petl/USB-C-cable-tester-C2C-caberQU/photos/v3/CaberQ_021.jpg

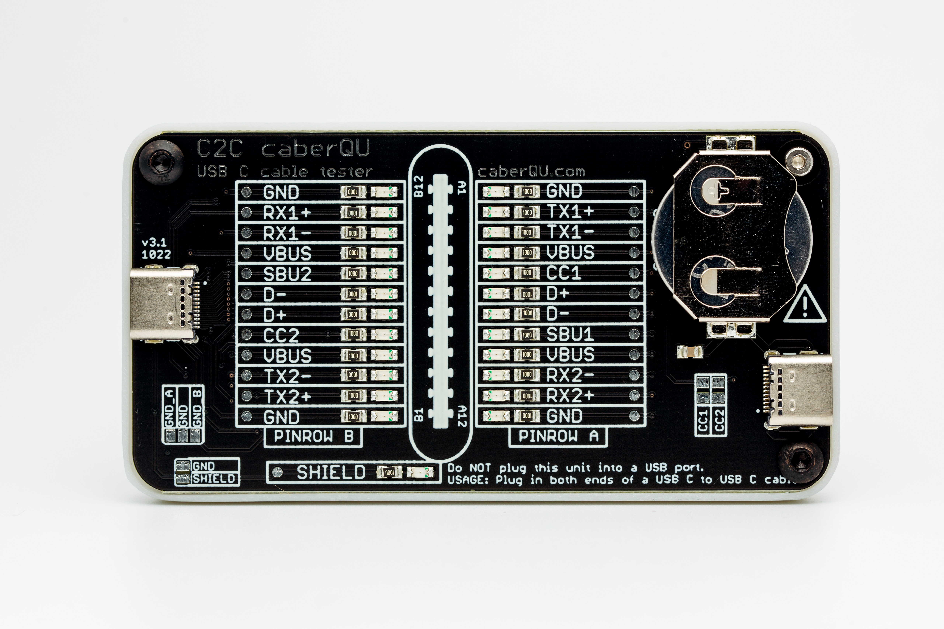
photos/v3/CaberQ_021.jpg
