petl/USB-C-cable-tester-C2C-caberQU/photos/v3/IMG_20220911_165947-min.jpg

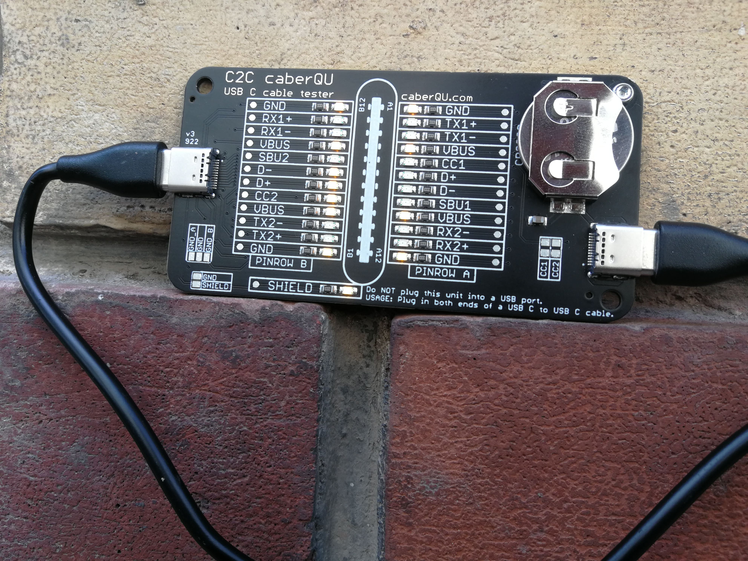
photos/v3/IMG_20220911_165947-min.jpg
