petl/USB-C-cable-tester-C2C-caberQU/documentation/v1/instructions_v1.png

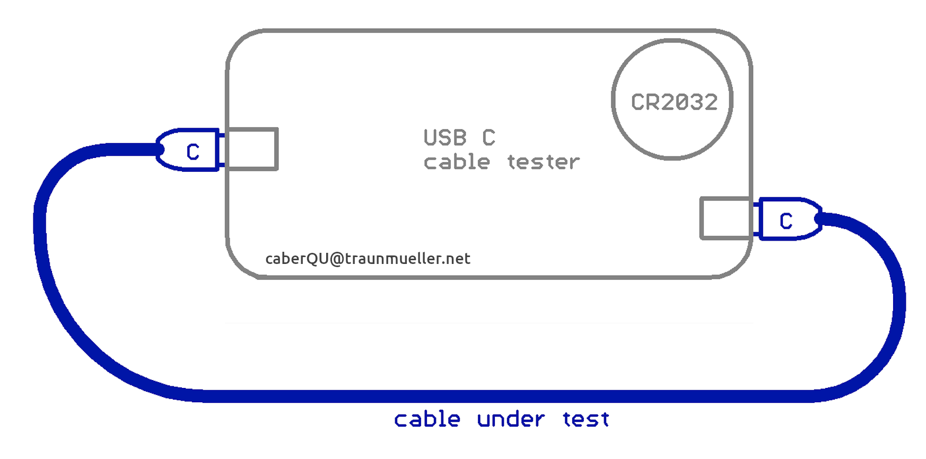
documentation/v1/instructions_v1.png
