petl/USB-C-cable-tester-C2C-caberQU/documentation/v1/2022_USB_C_cable_tester_v1.png

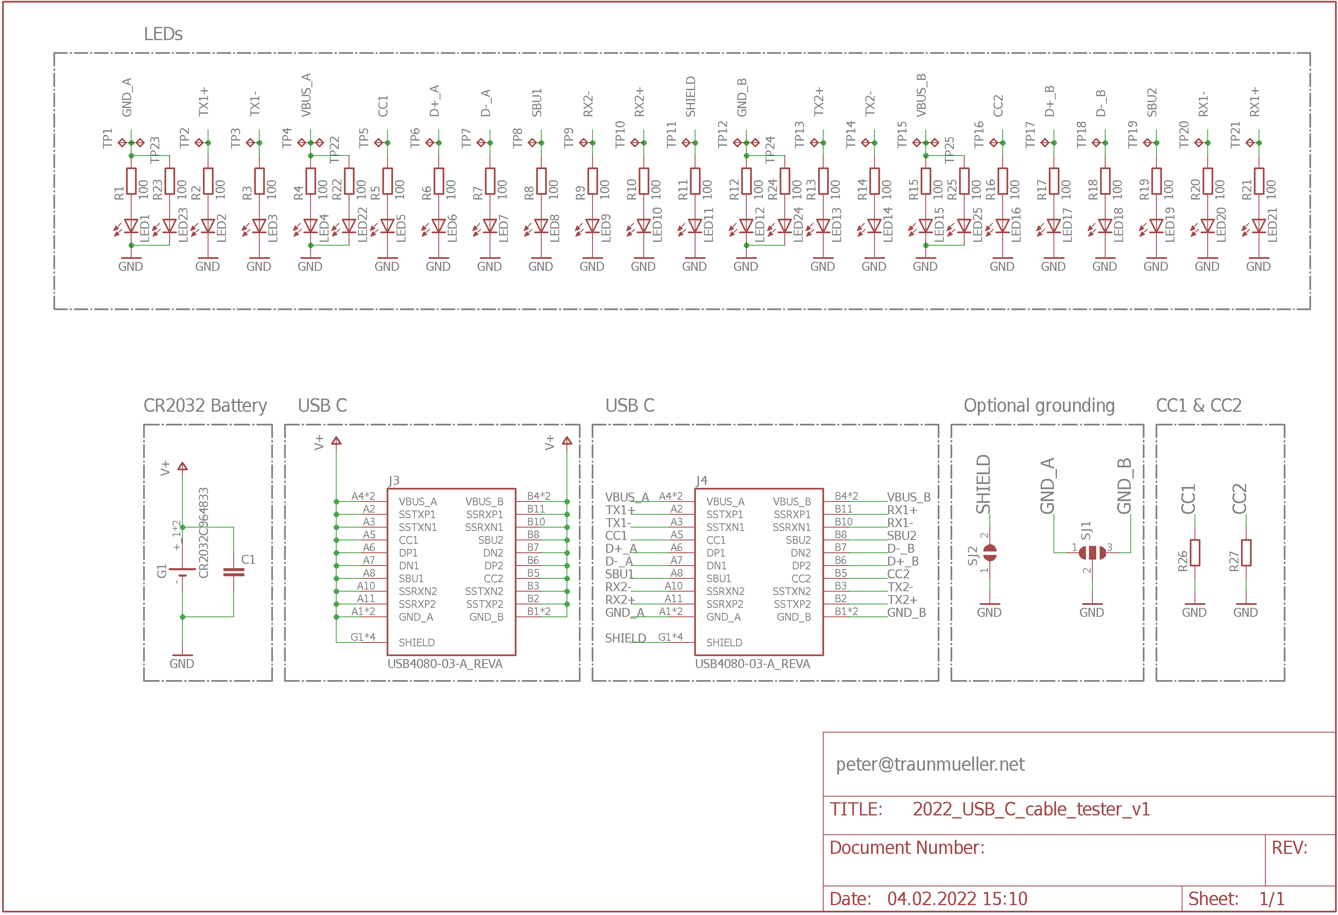
documentation/v1/2022_USB_C_cable_tester_v1.png
