petl/USB-C-cable-tester-C2C-caberQU/mechanics/drawing/2022_USB_C_cable_tester_v2_Kickstarter_crop.PNG

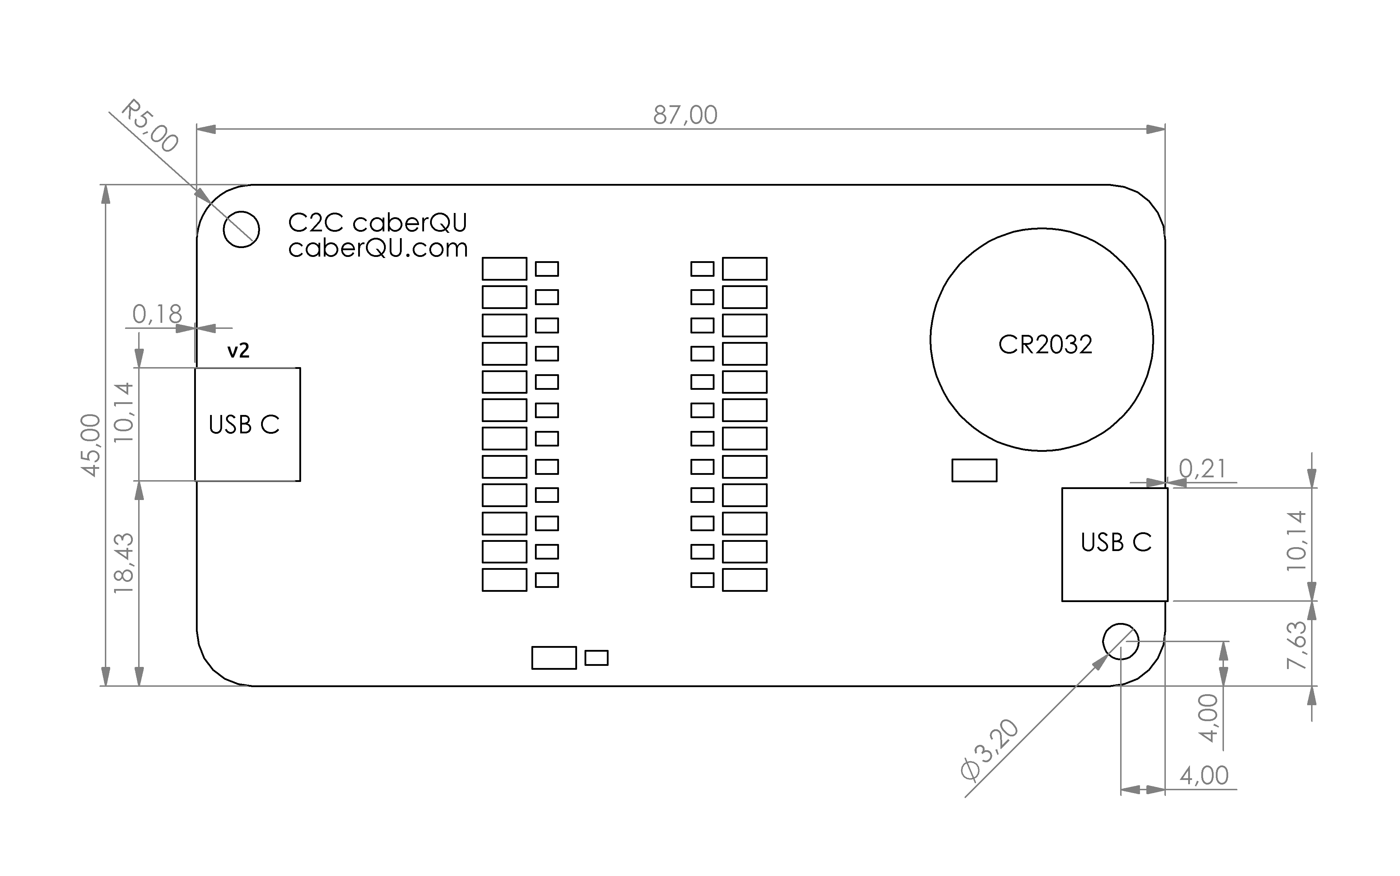
mechanics/drawing/2022_USB_C_cable_tester_v2_Kickstarter_crop.PNG
